antmicro/cvbs-mipi-bridge/assets/previews/layer0.png

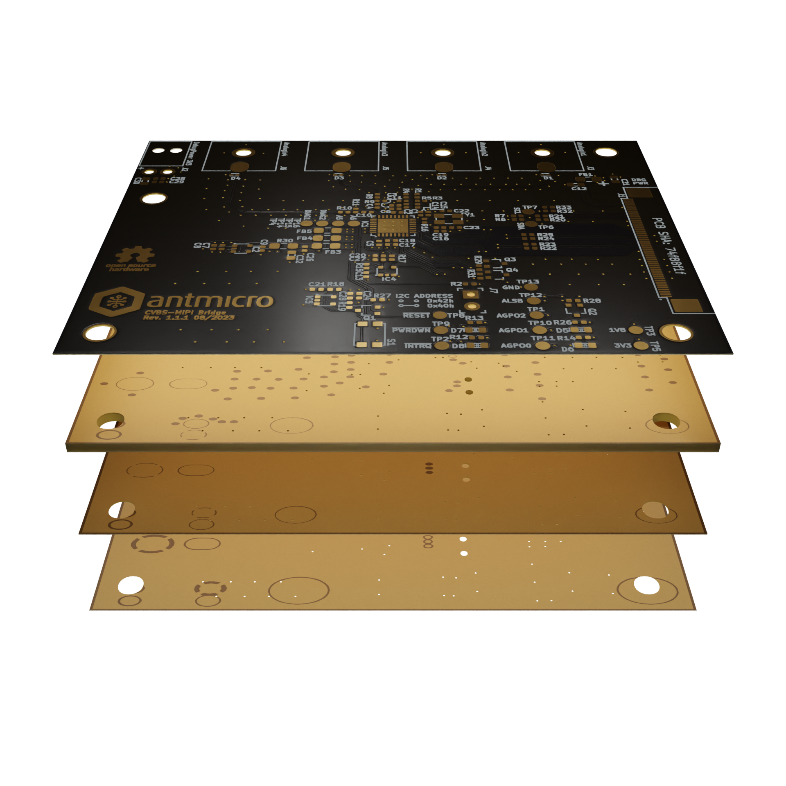
assets/previews/layer0.png
