antmicro/cvbs-mipi-bridge/assets/previews/layer0_thumbnail.webp

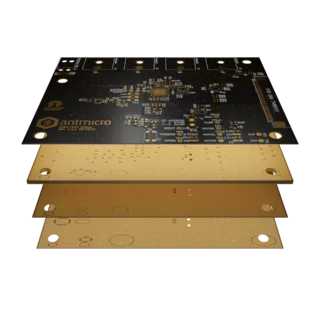
assets/previews/layer0_thumbnail.webp
