antmicro/cvbs-mipi-bridge/assets/previews/layer1_thumbnail.png

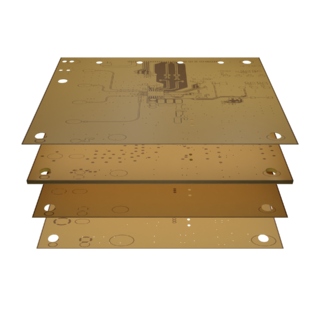
assets/previews/layer1_thumbnail.png
