antmicro/cvbs-mipi-bridge/assets/previews/layer2.png

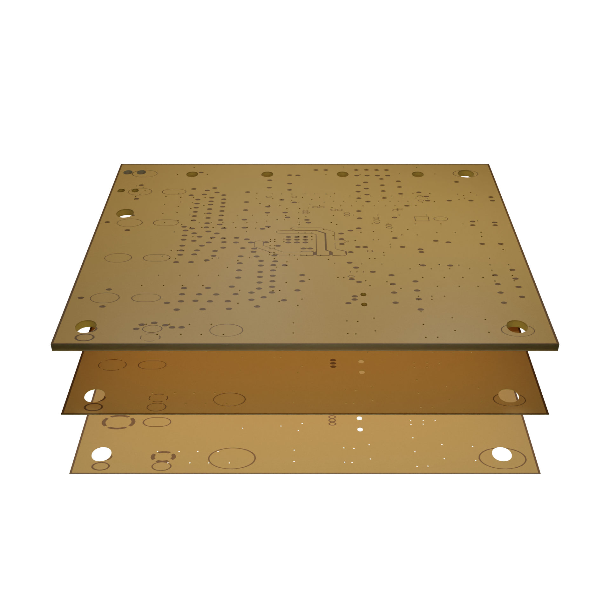
assets/previews/layer2.png
