antmicro/cvbs-mipi-bridge/assets/previews/layer2_thumbnail.png

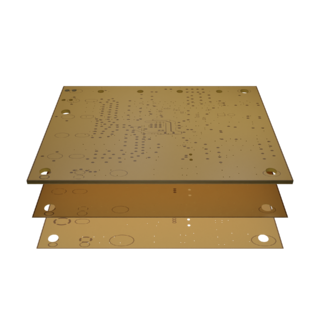
assets/previews/layer2_thumbnail.png
