antmicro/cvbs-mipi-bridge/assets/previews/layer3.png

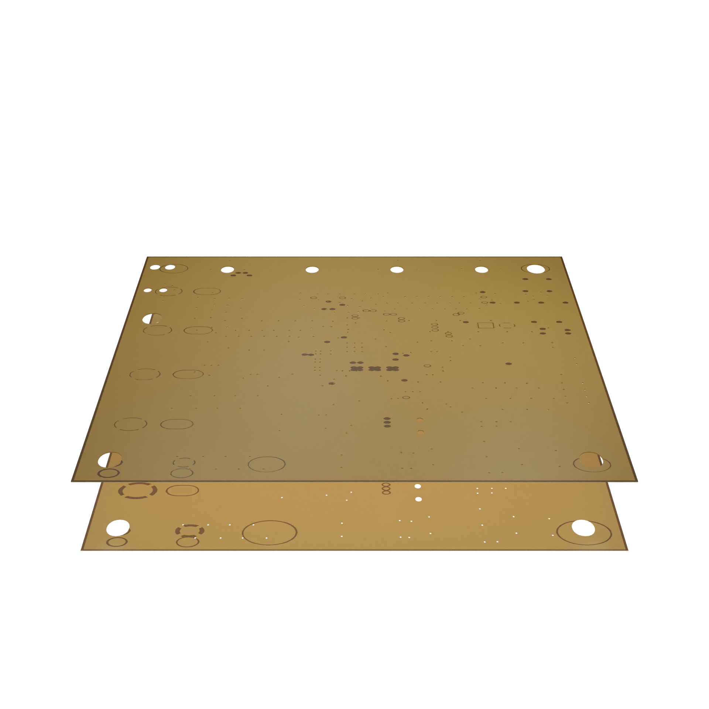
assets/previews/layer3.png
