antmicro/cvbs-mipi-bridge/assets/previews/leftB.png

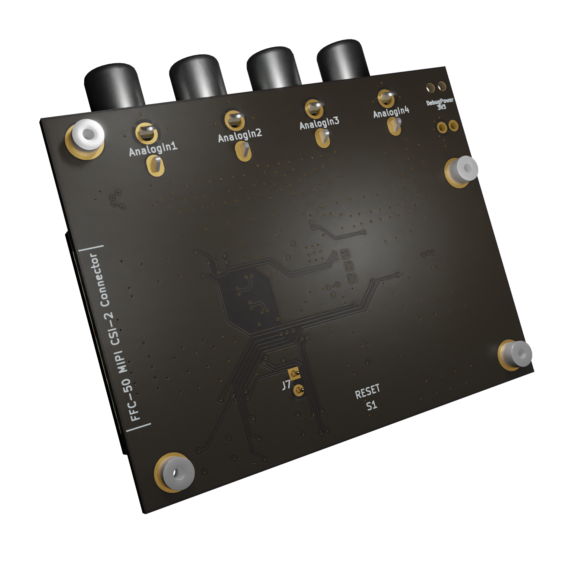
assets/previews/leftB.png
