antmicro/cvbs-mipi-bridge/assets/previews/leftT.png

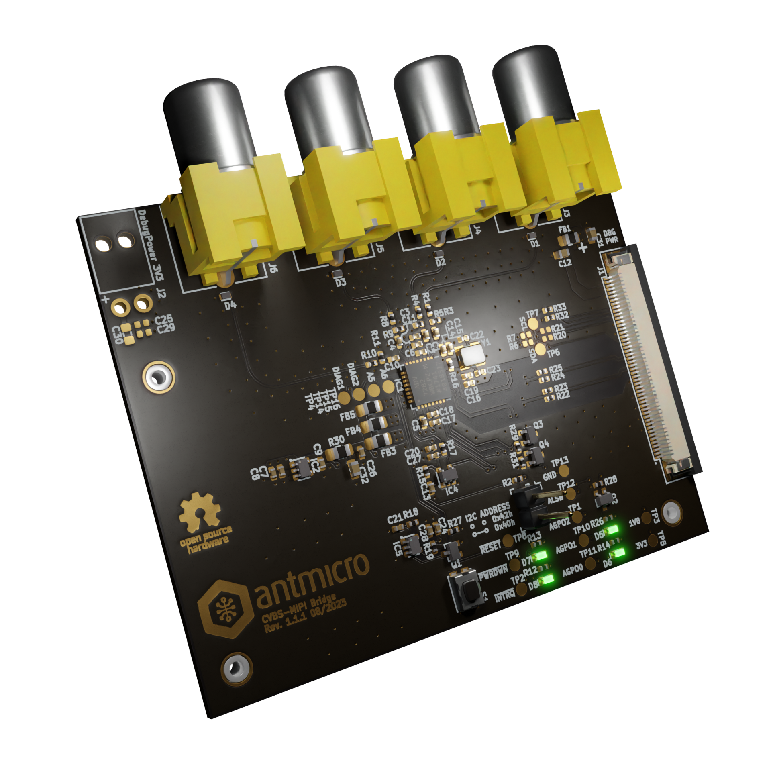
assets/previews/leftT.png
