antmicro/cvbs-mipi-bridge/assets/previews/orthoB.png

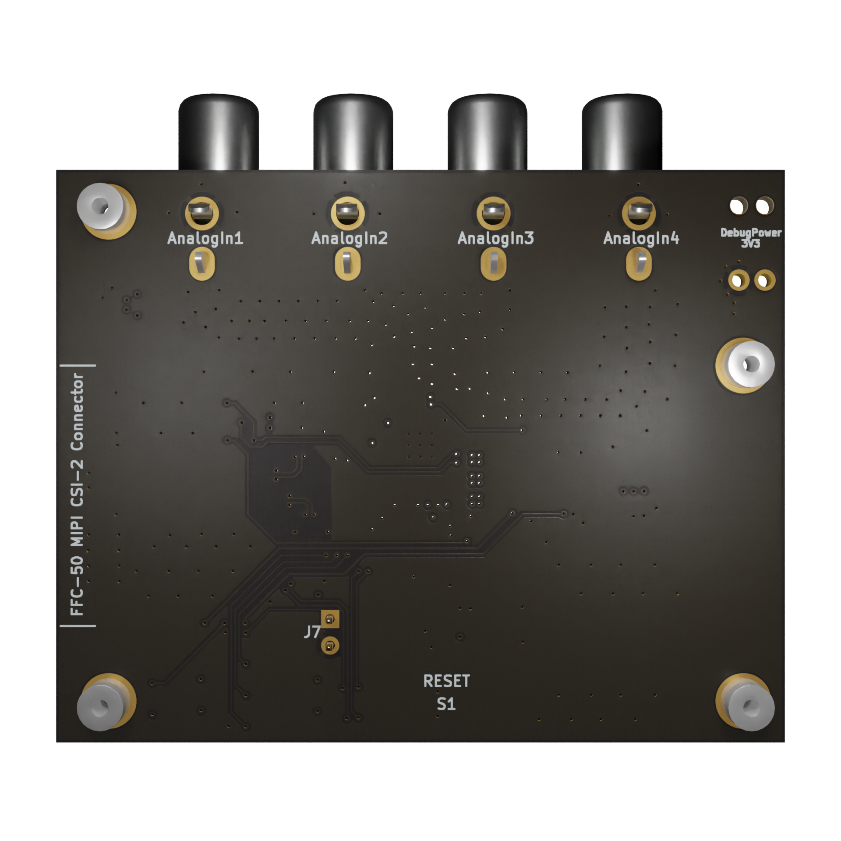
assets/previews/orthoB.png
