antmicro/cvbs-mipi-bridge/assets/previews/orthoT.png

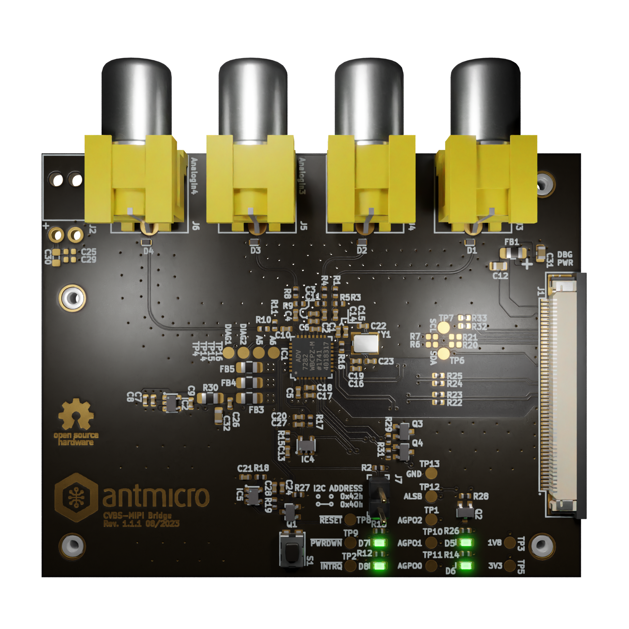
assets/previews/orthoT.png
