antmicro/cvbs-mipi-bridge/assets/previews/photoB.png

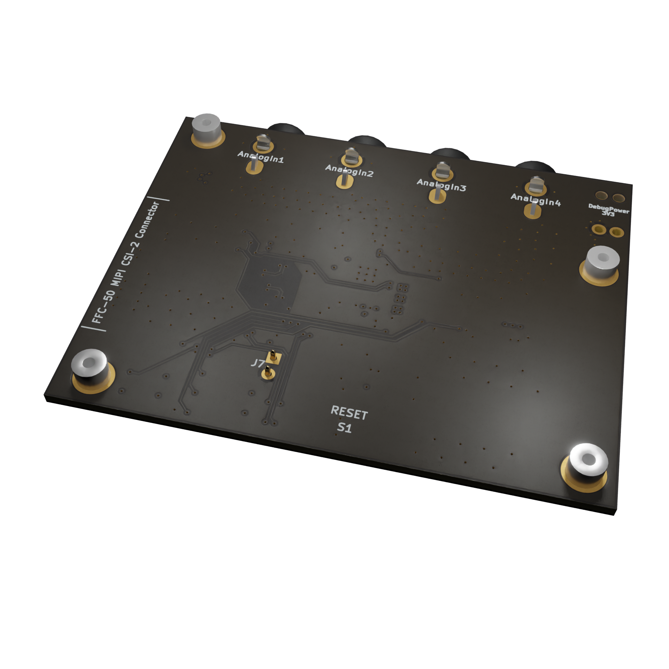
assets/previews/photoB.png
