antmicro/cvbs-mipi-bridge/assets/previews/photoT.png

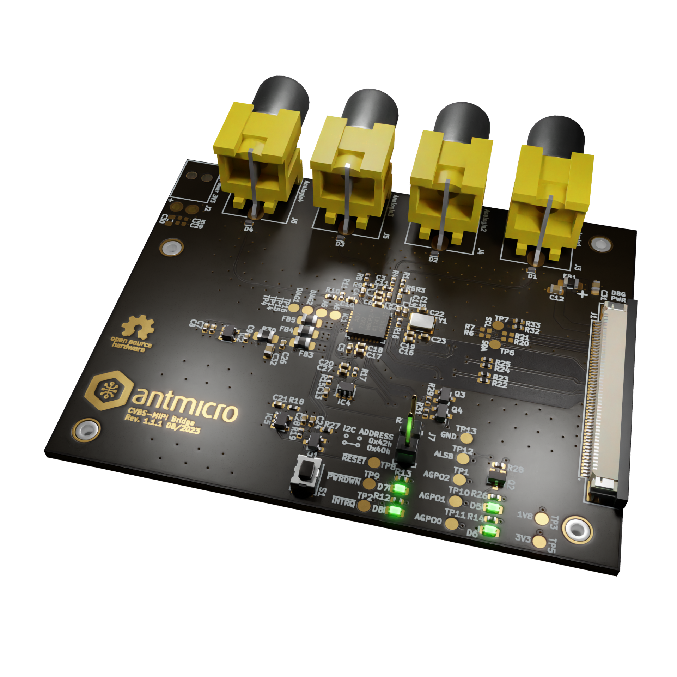
assets/previews/photoT.png
