antmicro/cvbs-mipi-bridge/assets/previews/rightB.png

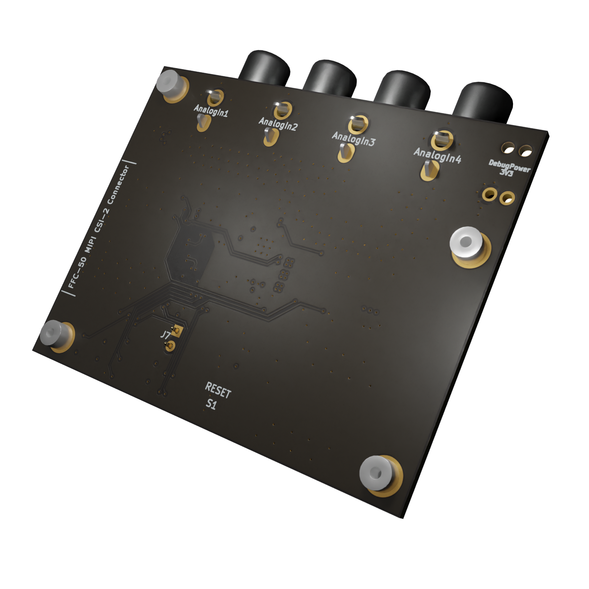
assets/previews/rightB.png
