antmicro/cvbs-mipi-bridge/assets/previews/rightT.png

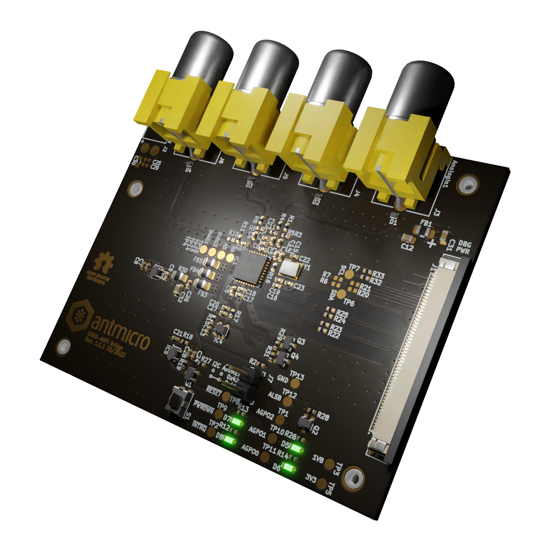
assets/previews/rightT.png
