antmicro/cvbs-mipi-bridge/assets/si/AIN1/S_11_smith.png

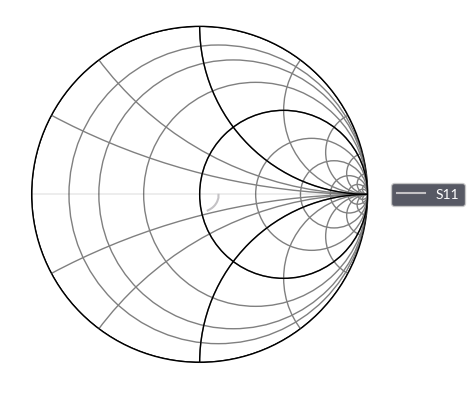
assets/si/AIN1/S_11_smith.png
