antmicro/cvbs-mipi-bridge/assets/si/AIN1/s_param_and_smith_1.png

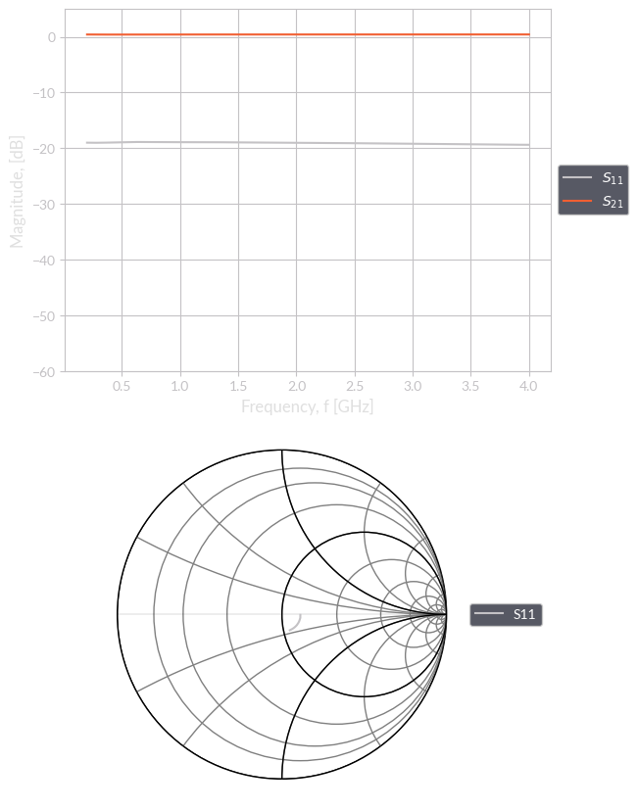
assets/si/AIN1/s_param_and_smith_1.png
