antmicro/cvbs-mipi-bridge/assets/si/AIN1/S_x1.png

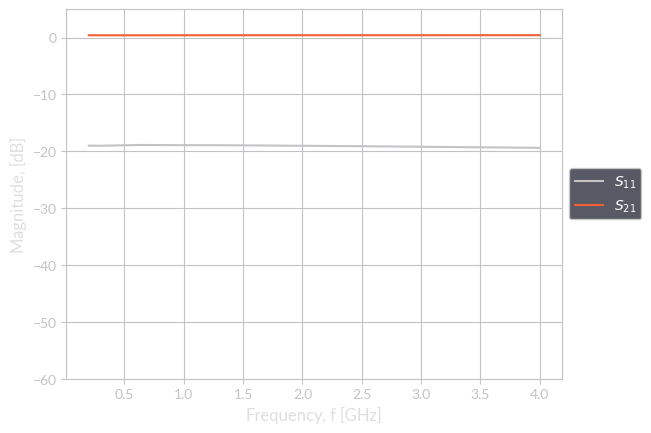
assets/si/AIN1/S_x1.png
