antmicro/cvbs-mipi-bridge/assets/si/AIN1/top_view.png

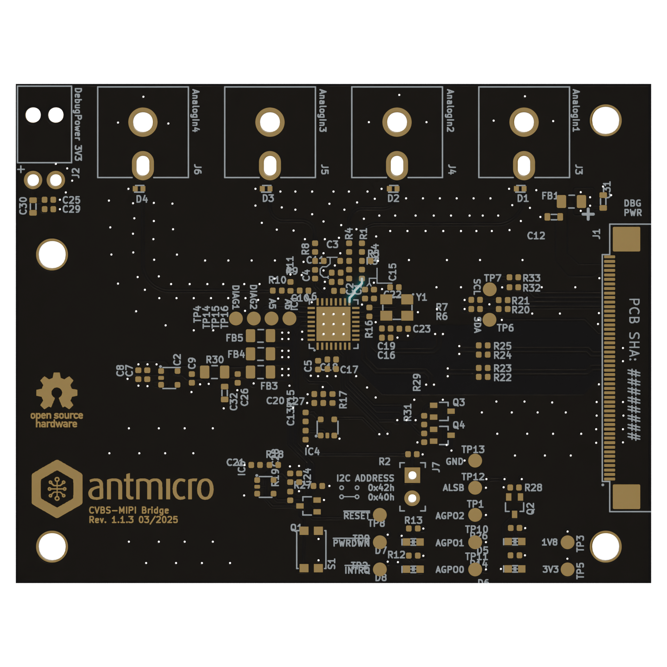
assets/si/AIN1/top_view.png
