antmicro/cvbs-mipi-bridge/assets/si/AIN1/Z_1.png

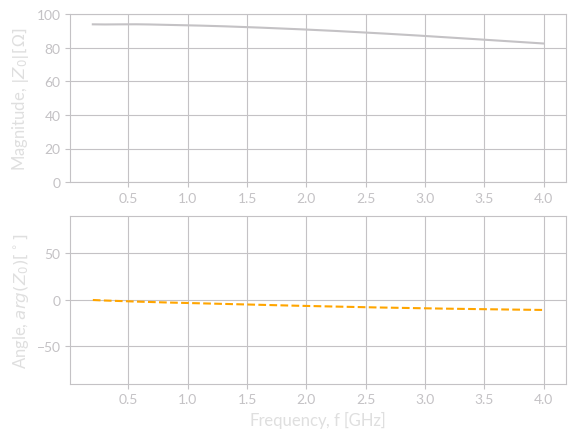
assets/si/AIN1/Z_1.png
