antmicro/cvbs-mipi-bridge/assets/si/AIN3/S_x1.png

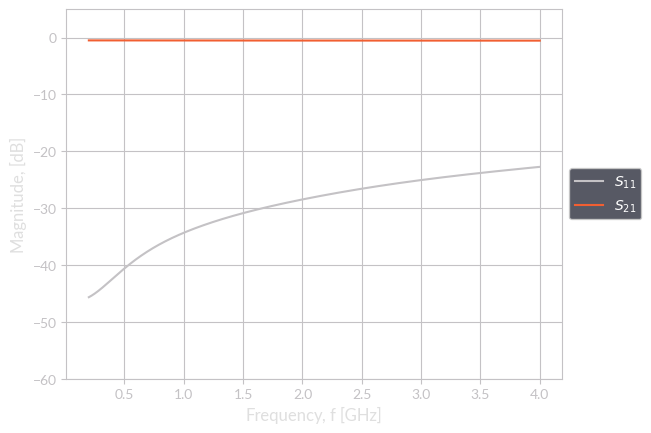
assets/si/AIN3/S_x1.png
