antmicro/cvbs-mipi-bridge/assets/si/AIN3_ESD/S_x1.png

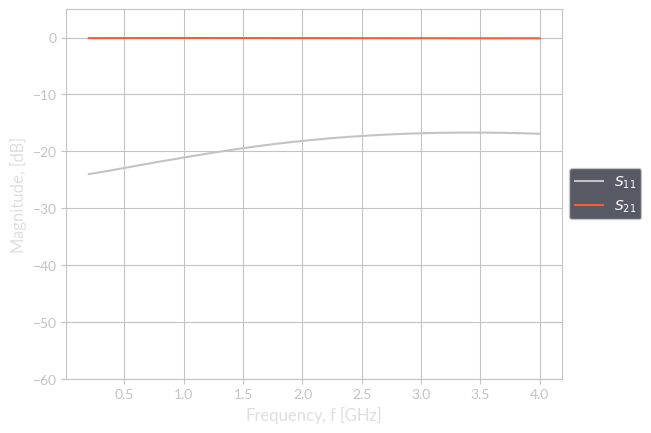
assets/si/AIN3_ESD/S_x1.png
