antmicro/cvbs-mipi-bridge/assets/si/CSI_A_CLK_Diff/diff_delay.png

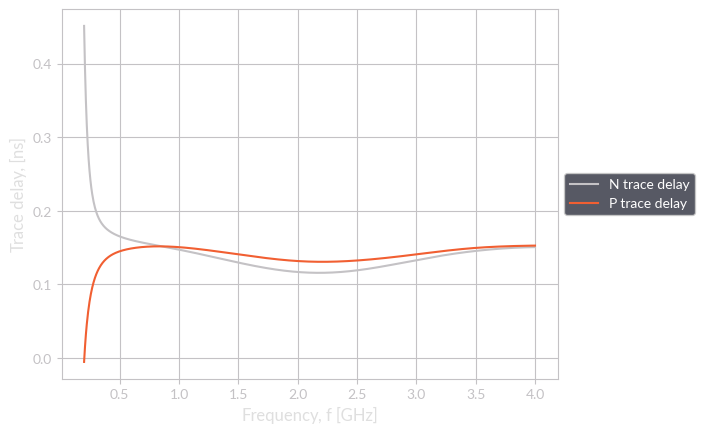
assets/si/CSI_A_CLK_Diff/diff_delay.png
