antmicro/cvbs-mipi-bridge/assets/si/CSI_A_CLK_Diff/s_param_and_smith_3.png

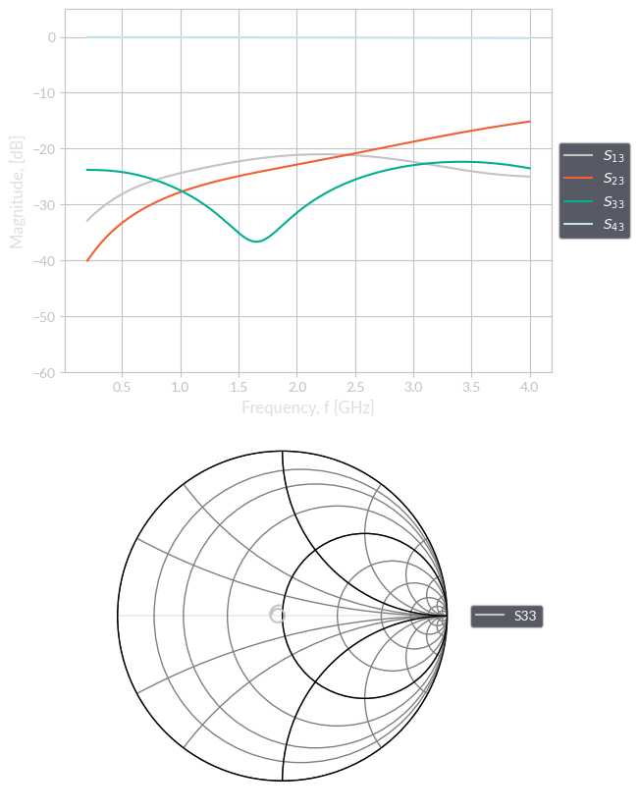
assets/si/CSI_A_CLK_Diff/s_param_and_smith_3.png
