antmicro/cvbs-mipi-bridge/assets/si/CSI_A_CLK_Diff/SDD_Diff.png

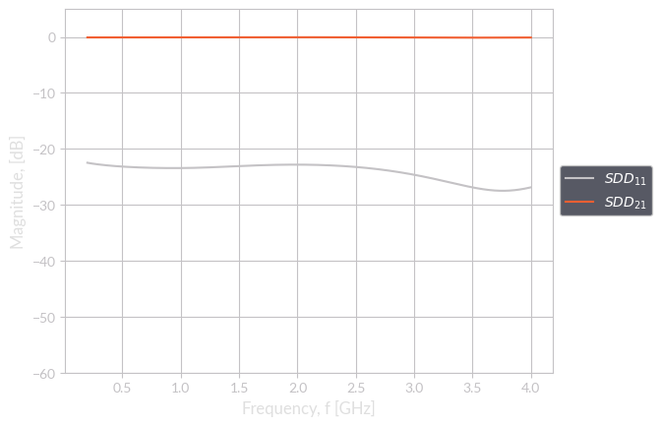
assets/si/CSI_A_CLK_Diff/SDD_Diff.png
