antmicro/cvbs-mipi-bridge/assets/si/CSI_A_CLK_Diff/Z_diff.png

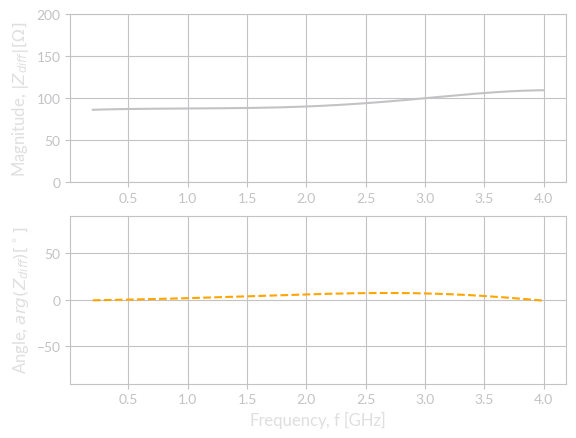
assets/si/CSI_A_CLK_Diff/Z_diff.png
