antmicro/cvbs-mipi-bridge/assets/si/CSI_A_D0_Diff/diff_delay.png

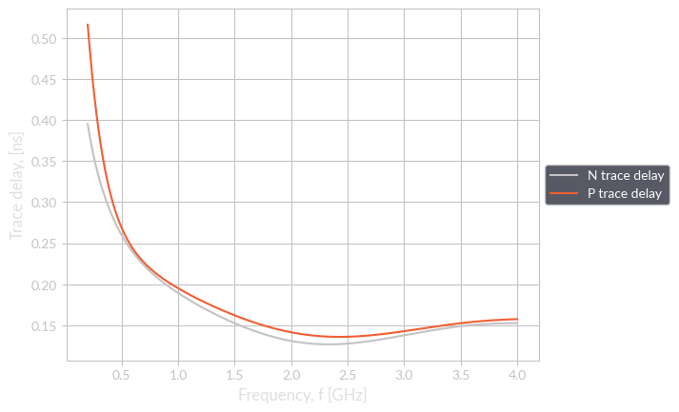
assets/si/CSI_A_D0_Diff/diff_delay.png
