antmicro/cvbs-mipi-bridge/assets/si/CSI_A_D0_Diff/s_param_and_smith_3.png

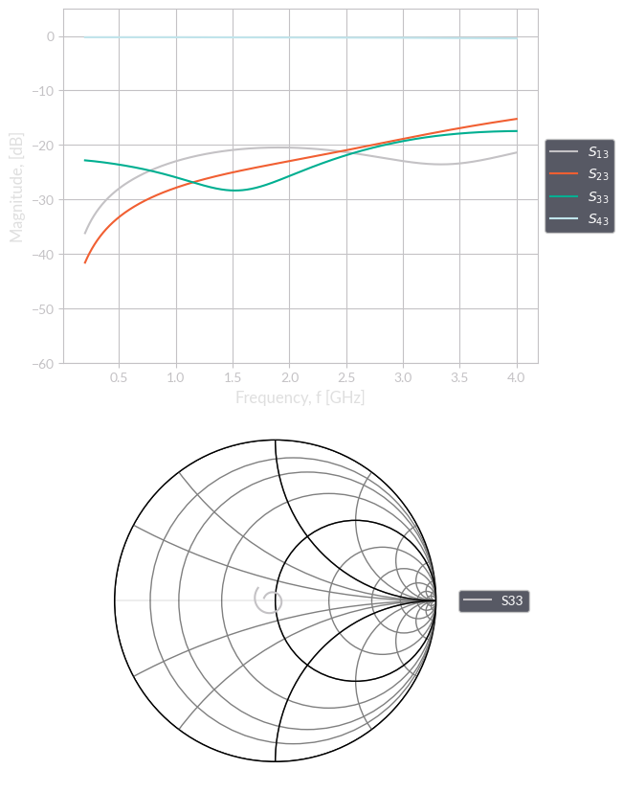
assets/si/CSI_A_D0_Diff/s_param_and_smith_3.png
