antmicro/cvbs-mipi-bridge/assets/si/CSI_A_D0_Diff/S_x3.png

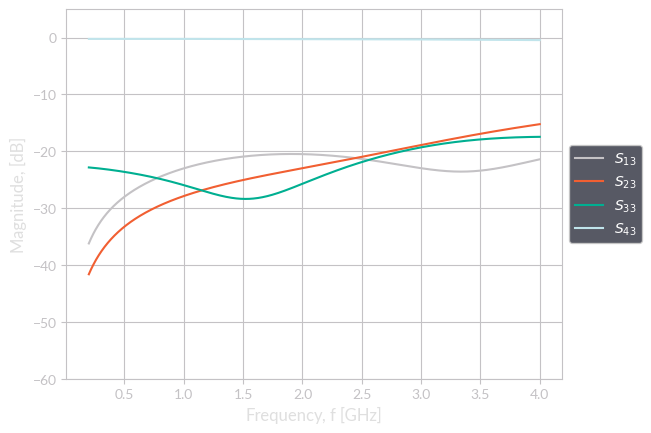
assets/si/CSI_A_D0_Diff/S_x3.png
