antmicro/cvbs-mipi-bridge/assets/si/Net-J1-Pad40/S_x1.png

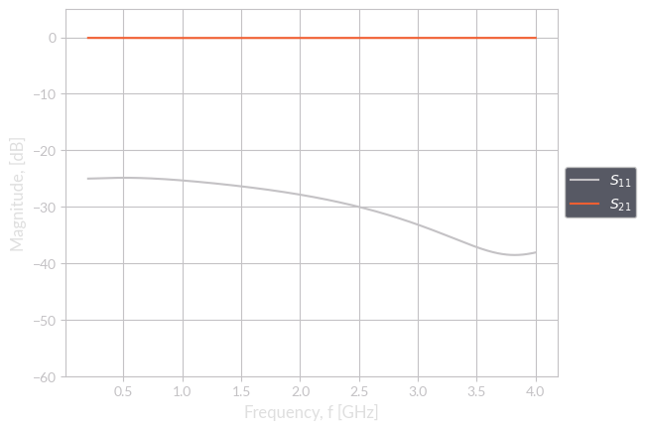
assets/si/Net-J1-Pad40/S_x1.png
